congoblue/avoremote/templatebox.scad

// Definition size of housing
// **************************

       // Those settings have to be identical to the cover !!!
width_x      = 205;          // Width of the housing (outer dimension) 
debth_y      = 100;           // Debth of the housing (outer dimension)
wall         = 1.8;          // Wall thickness of the box
cornerradius = 4.0;          // Radius of the corners
                             //   This value also defines the posts for stability and
                             //   for the press-in nuts!

       // Those settings are more or less independent from the cover
height_z     = 25;           // Heigth of the lower part. Total height is this value plus
                             //   the height of the cover
plate        = 1.4;          // Thickness of the bottom plain

       //Definition size of press-in nuts
nutdiameter  = 4.0;          // Hole diameter for thermal press-in nut
nutlength    = 10;          // Depth of the nut hole


//Definition of circle angular resolution
resol        = 36;



difference () {

// Construction of housing
   union () {
   // Definition of main body
      difference () {
         union () {
            cube ( [width_x, debth_y - (2* cornerradius), height_z], center = true );
            cube ( [width_x - (2* cornerradius), debth_y, height_z], center = true );
         };
         translate ( [0,0, plate / 2] ){
            cube ( [width_x - (2* wall), debth_y- (2* wall), height_z - plate], center = true ); 
         };
      };

      // Construction of four corner cylinders including nut holes
      // 1st quadrant
      translate ( [(width_x / 2) - cornerradius, (debth_y / 2) - cornerradius, 0 ] ) {
         difference () {
            cylinder (h=height_z, r=cornerradius, center = true, $fn = resol);
            translate ( [ 0,0,(height_z / 2)-(nutlength / 2) ] ) {
               cylinder (h = nutlength, r = nutdiameter / 2, center = true, $fn = resol);
            };
         };
      };

      // 2nd quadrant
      translate ( [-(width_x / 2) + cornerradius, (debth_y / 2) - cornerradius, 0] ) {
         difference () {
            cylinder (h=height_z, r=cornerradius, center = true, $fn = resol);
            translate ( [ 0,0,(height_z / 2)-(nutlength / 2) ] ) {
               cylinder (h = nutlength, r = nutdiameter / 2, center = true, $fn = resol);
            };
         };
      };

      // 4th quadrant
      translate ( [(width_x / 2) - cornerradius, -(debth_y / 2) + cornerradius, 0] ) {
         difference () {
            cylinder (h=height_z, r=cornerradius, center = true, $fn = resol);
            translate ( [ 0,0,(height_z / 2)-(nutlength / 2) ] ) {
               cylinder (h = nutlength, r = nutdiameter / 2, center = true, $fn = resol);
            };
         };
      };

      // 3rd quadrant
      translate ( [-(width_x / 2) + cornerradius, -(debth_y / 2) + cornerradius, 0] ) {
         difference () {
            cylinder (h=height_z, r=cornerradius, center = true, $fn = resol);
            translate ( [ 0,0,(height_z / 2)-(nutlength / 2) ] ) {
               cylinder (h = nutlength, r = nutdiameter / 2, center = true, $fn = resol);
            };
         };
      }; 
   };

// Space for the construction of holes, breakouts, ... 

    //hole for usb
    translate ([-width_x/2+54,debth_y/2,-5.5]) cube ([12,20,7],center=true);


};
